xuminic/woodshed/05_interior/figure_stud_adhesive.jpg

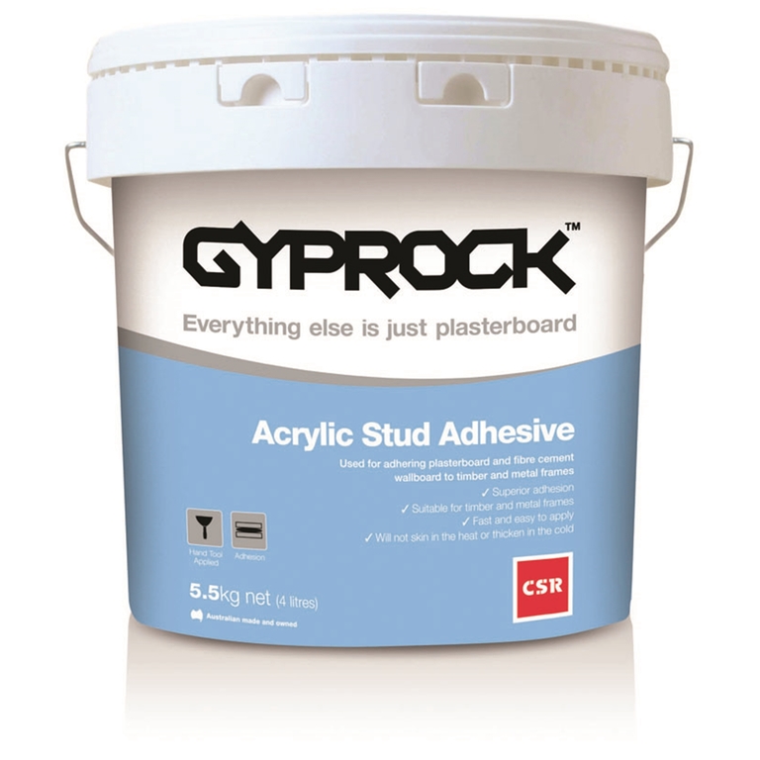
05_interior/figure_stud_adhesive.jpg
